anthonyneedles/QAZ/src/usb/consumer_usb_desc.cpp

/**
 * @file      consumer_usb_desc.cpp
 * @brief     USB descriptor management
 *
 * @author    Anthony Needles
 * @date      2020/11/26
 * @copyright (c) 2020 Anthony Needles. GNU GPL v3 (see LICENSE)
 *
 * This module defines all of the USB descriptors (device, config, report, etc.) for a given device.
 * The information for a descriptor can then be obtained via API.
 */

#include "usb/consumer_usb_desc.hpp"

#include "util/debug.hpp"
#include "util/expressions.hpp"

namespace {

/// Device descriptor. Contains basic information about the device and specify string desc indicies.
constexpr uint8_t DESCRIPTOR_DEVICE[] = {
      18,        // bLength
       1,        // bDescriptorType        Device
    0x00, 0x02,  // bcdUSB                 USB 2.0
    0x00,        // bDeviceClass           Interface defined
    0x00,        // bDeviceSubClass
    0x00,        // bDeviceProtocol
      64,        // bMaxPacketSize         64 bytes
    0x1D, 0xC0,  // idVendor               0xC01D
    0x22, 0xAB,  // idProduct              0xAA22
    0x00, 0x01,  // bcdDevice              1.00
       1,        // iManufacturer          'anthonyneedles'
       2,        // iProduct               'qaz media'
       0,        // iSerialNumber
       1,        // bNumConfigurations
};

/// Configuration, Interface, HID, and Endpoint  descriptors. These are eventually asked for, all at
/// once. These define the device interface as USB HID Keyboard, the report size, and the interrupt
/// endpoint config.
constexpr uint8_t DESCRIPTOR_CONFIG[] = {
// Configuration Descriptor
       9,        // bLength
       2,        // bDescriptorType        Configuration
      34, 0x00,  // wTotalLength           9 + 9 + 9 + 7
       1,        // bNumInterfaces
       1,        // bConfigurationValue    Set Configuration argument
       0,        // iConfiguration         No string
    0x80,        // bmAttributes           Bus powered, no wake-up
     250,        // bMaxPower              250*2 = 500 mA
// Interface Descriptor
       9,        // bLength
       4,        // bDescriptorType        Interface
       0,        // bInterfaceNumber
       0,        // bAlternateSetting
       1,        // bNumEndpoints
    0x03,        // bInterfaceClass        HID
    0x01,        // bInterfaceSubClass     Boot
    0x00,        // bInterfaceProtocol     No specific protocol
       0,        // iInterface             No string
// HID Descriptor
       9,        // bLength
    0x21,        // bDescriptorType        HID
    0x11, 0x01,  // bcdHID                 HID 1.11
    0x00,        // bCountryCode           Not localized
       1,        // bNumDescriptors
    0x22,        // bDescriptorType        Report
      38, 0x00,  // wDescriptorLength      38 bytes
// Endpoint 1 In Descriptor
       7,        // bLength
       5,        // bDescriptorType        Endpoint
    0x81,        // bEndpointAddress       1, In
    0x03,        // bmAttributes           Interrupt
       2, 0x00,  // wMaxPacketSize         2 bytes
      10,        // bInterval              10 ms
};

/// Language String Descriptor (index 0). Our string descs are in English.
constexpr uint8_t DESCRIPTOR_LANG[] = {
       4,        // bLength                2 + 2*2
       3,        // bDescriptorType        String
    0x09, 0x04,  // wLANGID[0]             English (US)
};

/// Manufactrurer String Descriptor (index 1). In Unicode format.
constexpr uint8_t DESCRIPTOR_MANUFACT[] = {
      30,         // bLength                2 + 14*2
       3,         // bDescriptorType        String
      'a', 0x00,  // wString                anthonyneedles
      'n', 0x00,
      't', 0x00,
      'h', 0x00,
      'o', 0x00,
      'n', 0x00,
      'y', 0x00,
      'n', 0x00,
      'e', 0x00,
      'e', 0x00,
      'd', 0x00,
      'l', 0x00,
      'e', 0x00,
      's', 0x00,
};

/// Product String Descriptor (index 2). In Unicode format.
constexpr uint8_t DESCRIPTOR_PRODUCT[] = {
      20,         // bLength                2 + 9*2
       3,         // bDescriptorType        String
      'q', 0x00,  // wString                qaz keyboard
      'a', 0x00,
      'z', 0x00,
      ' ', 0x00,
      'm', 0x00,
      'e', 0x00,
      'd', 0x00,
      'i', 0x00,
      'a', 0x00,
};

/// HID Report Descriptor. Defines the format of key packets we send.
constexpr uint8_t DESCRIPTOR_HIDREPORT[] = {
    0x05, 0x0C,  // Usage Page   = Consumer Devices,
    0x09, 0x01,  // Usage        = Consumer Control,
    0xA1, 0x01,  // Collection   = Application,
    0x05, 0x0C,  //   Usage Page   = Consumer Devices,
    0x15, 0x00,  //   Logical Min  = 0
    0x25, 0x01,  //   Logical Max  = 1
    0x75, 0x01,  //   Report Size  = 1
    0x95, 0x07,  //   Report Count = 7
    0x09, 0xB5,  //   Usage        = Bit 0: Scan Next Track     (0xB5)
    0x09, 0xB6,  //   Usage        = Bit 1: Scan Previous Track (0xB6)
    0x09, 0xB7,  //   Usage        = Bit 2: Stop                (0xB7)
    0x09, 0xCD,  //   Usage        = Bit 3: Play / Pause        (0xCD)
    0x09, 0xE2,  //   Usage        = Bit 4: Mute                (0xE2)
    0x09, 0xE9,  //   Usage        = Bit 5: Volume Up           (0xE9)
    0x0A,        //   Usage        = Bit 6: Volume Down         (0x00EA)
    0xEA, 0x00,
    0x81, 0x02,  //   Input        = Data, Var, Abs
    0x95, 0x09,  //   Report Count = 9, Bits 7-15: N/A
    0x81, 0x01,  //   Input        = Constant
    0xC0         // End Collection
};

/// Descriptor table entry, pairing the desc ID with desc info
struct USBDescTableEntry{
    uint16_t id;
    usb_desc::USBDesc desc;
};

/// Descriptor table, with an entry for each descriptor
constexpr USBDescTableEntry desc_table[] = {
    { usb_desc::DEVICE_ID,    { DESCRIPTOR_DEVICE,    sizeof(DESCRIPTOR_DEVICE)    } },
    { usb_desc::CONFIG_ID,    { DESCRIPTOR_CONFIG,    sizeof(DESCRIPTOR_CONFIG)    } },
    { usb_desc::LANG_ID,      { DESCRIPTOR_LANG,      sizeof(DESCRIPTOR_LANG)      } },
    { usb_desc::MANUFACT_ID,  { DESCRIPTOR_MANUFACT,  sizeof(DESCRIPTOR_MANUFACT)  } },
    { usb_desc::PRODUCT_ID,   { DESCRIPTOR_PRODUCT,   sizeof(DESCRIPTOR_PRODUCT)   } },
    { usb_desc::HIDREPORT_ID, { DESCRIPTOR_HIDREPORT, sizeof(DESCRIPTOR_HIDREPORT) } },
};

}  // namespace

/**
 * @brief For obtaining descriptors
 *
 * Information for a given descriptor can be requested with this, and (if exists) a pointer to the
 * desc buffer and the size (in bytes) is returned via `desc`.
 *
 * @param[in]     desc_id  ID of requested descriptor
 * @param[in,out] desc     Descriptor information struct that will be populated (if `desc_id` valid)
 *
 * @return 0 if success, -1 if descriptor is not defined
 */
int usb_desc::get_desc(uint16_t desc_id, USBDesc *desc)
{
    int ret = -1;

    for (unsigned i = 0; i < COUNT_OF(desc_table); ++i) {
        if (desc_table[i].id == desc_id) {
            desc->buf_ptr = desc_table[i].desc.buf_ptr;
            desc->size    = desc_table[i].desc.size;
            ret = 0;
            break;
        }
    }

    if (ret == -1) {
        debug::printf("ERROR: Requested undefined descriptor (%d)\r\n", desc_id);
    }

    return ret;
}
