anthonyneedles/QAZ/src/keyboard/key_matrix.hpp

/**
 * @file      key_matrix.hpp
 * @brief     Implements key matrix scanning
 *
 * @author    Anthony Needles
 * @date      2020/10/04
 * @copyright (c) 2020 Anthony Needles. GNU GPL v3 (see LICENSE)
 *
 * Used to detect keypress on a key matrix. The columns open drain outputs, and the rows are inputs
 * with the pull ups. Under normal circumstances, the columns are high-Z, and the rows will read
 * VCC. When scanning, each column is driven to GND, and so each row with a pressed key will read
 * GND.
 *
 * Two keypress functionality exist in this module:
 *   1. Constantly pressed key buffering
 *
 *   The key in buffer is filled with every key currently pressed. This is what USB HID wants.
 *   Functionality to get this buffer is TBD.
 *
 *   2. Single callback key presses
 *
 *   For specified keys, a callback function will be called ONCE per key press, so the user needs
 *   to release the key and press it again for the callback to be called again. This is useful for
 *   user keys, such as changing the RGB LED color, brightness, etc.
 */

#ifndef KEYBOARD_KEY_MATRIX_HPP_
#define KEYBOARD_KEY_MATRIX_HPP_

#include <cstdint>

#include "bsp/bsp.hpp"
#include "stm32f0xx.h"  // NOLINT

/**
 * @brief Key Matrix namespace
 *
 * This namespace pertains to the detection of keys pressed in a key matrix, and the generation
 * of weak callback functions for each key with callback functionality.
 */
namespace keymatrix {

/// Keys that can be detected at once
constexpr unsigned KEY_BUF_SIZE = 6;

/// Get the keycode from a symbol
#define KEY(x) (HID_USAGE_KEYBOARD_##x)

/// Weak callbacks for each of the callback keys. These are called ONCE PER BUTTON PRESS. The user
/// must release then repress the key for a second call
#define K(symbol) __WEAK void callback_##symbol(void);
CALLBACK_KEY_TABLE(K)
#undef K

/// Keycodes in HID standard are 16-bit values
typedef int16_t Key;

/// Init all rows as pullup inputs and columns as open-drain outputs
void init(void);

/// Run scan routine, fill internal key buffer, and call any key callbacks
void task(void);

/// Fills input buffer (OF SIZE `KEY_BUF_SIZE`) with current key buffer
void copy_key_buffer(Key *key_buf);

/// Returns whether the keyboard is idle (no keypresses)
bool is_idle(void);

}  // namespace keymatrix

#endif  // KEYBOARD_KEY_MATRIX_HPP_
