anthonyneedles/QAZ/src/core/clock.hpp

/**
 * @file      clock.hpp
 * @brief     System clock initialization
 *
 * @author    Anthony Needles
 * @date      2020/10/12
 * @copyright (c) 2020 Anthony Needles. GNU GPL v3 (see LICENSE)
 *
 * Holds any user clock configuration that should be applied before any other user initialization
 * or project execution.
 */

#ifndef CORE_CLOCK_HPP_
#define CORE_CLOCK_HPP_

#include <cstdint>

/**
 * @brief Clock namespace
 *
 * Holds configuration for the MCU clocking.
 */
namespace clock {

/// The (after init) frequency of the core clock SYSCLK
constexpr uint32_t SYSCLK_HZ = 48000000;

/// Init system clock for HSE
void init(void);

}  // namespace clock

#endif  // CORE_CLOCK_HPP_
